SunboX/CO2-Ampel/Fotos/PXL_20201120_171447226.jpg

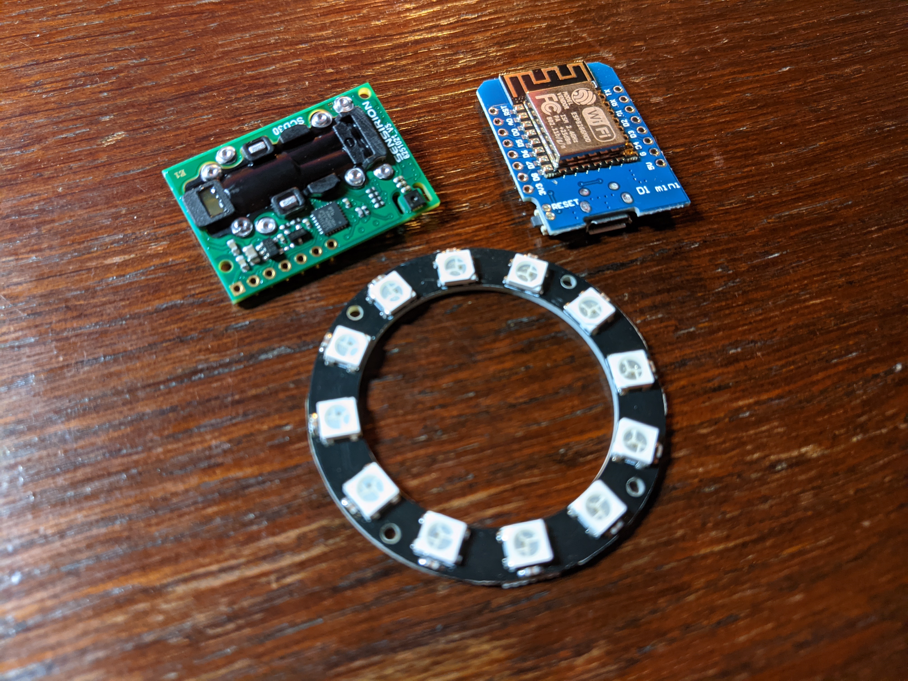
Fotos/PXL_20201120_171447226.jpg
