SunboX/CO2-Ampel/Fotos/PXL_20201120_172152929.jpg

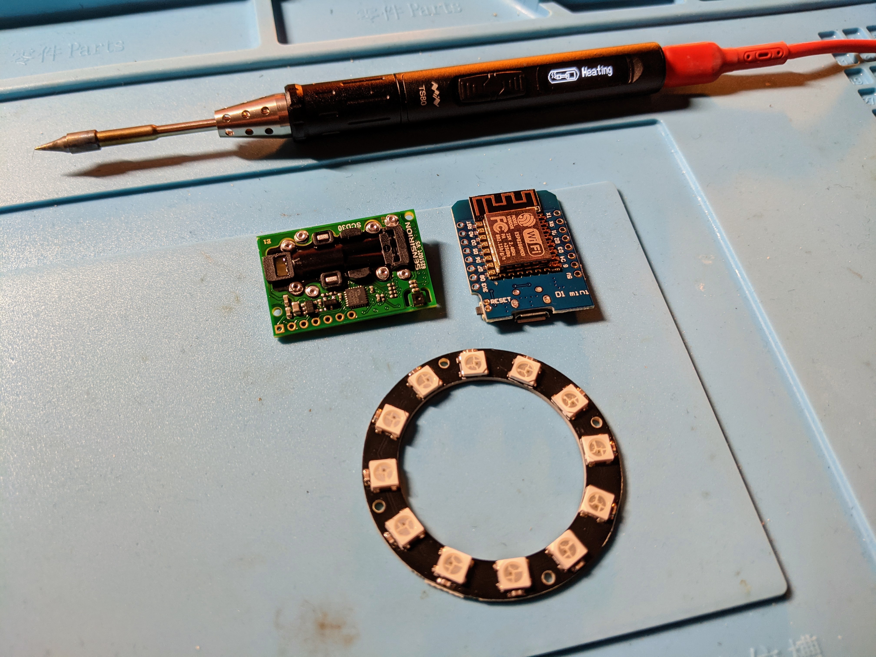
Fotos/PXL_20201120_172152929.jpg
