SunboX/CO2-Ampel/Fotos/PXL_20201120_174045806.jpg

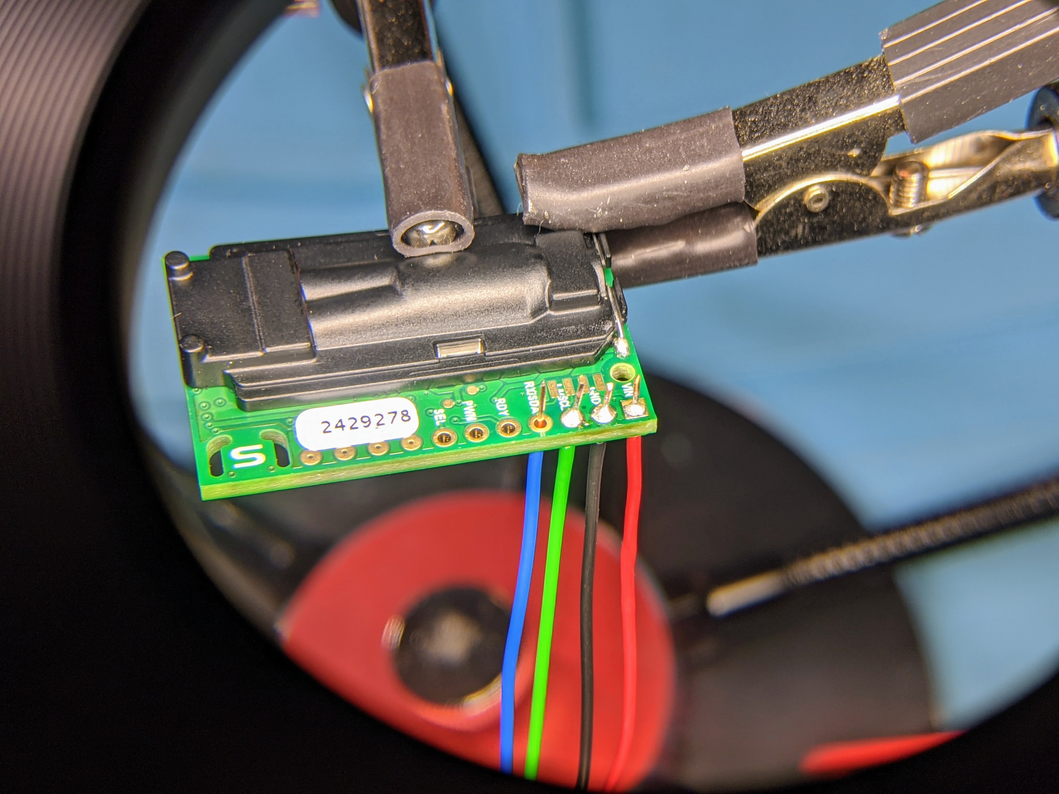
Fotos/PXL_20201120_174045806.jpg
