SunboX/CO2-Ampel/Fotos/PXL_20201120_174952225.jpg

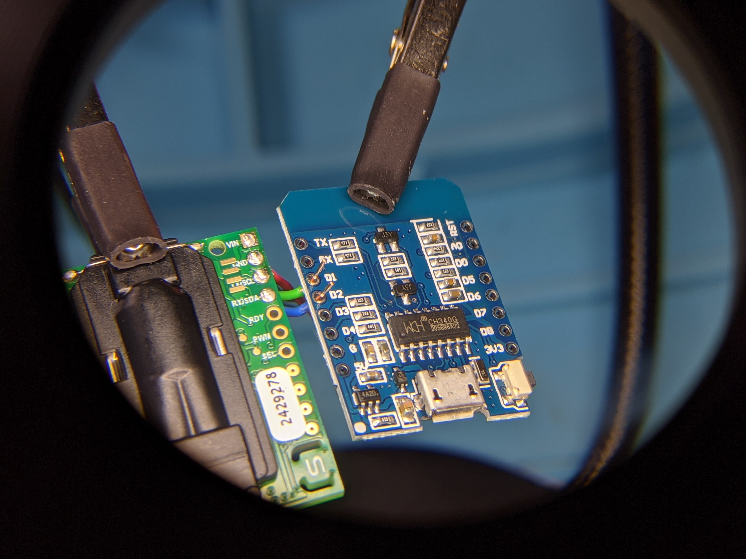
Fotos/PXL_20201120_174952225.jpg
