SunboX/CO2-Ampel/Fotos/PXL_20201120_175120646.jpg

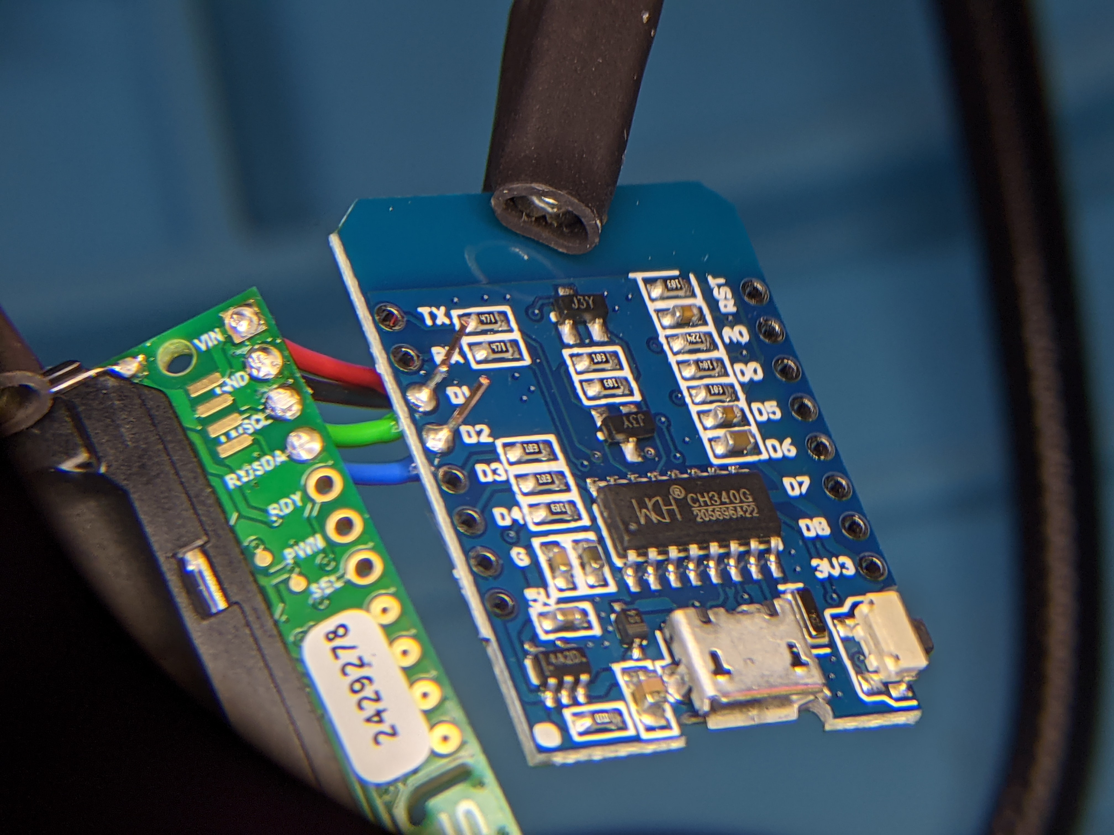
Fotos/PXL_20201120_175120646.jpg
