SunboX/CO2-Ampel/Fotos/PXL_20201121_131157792.jpg

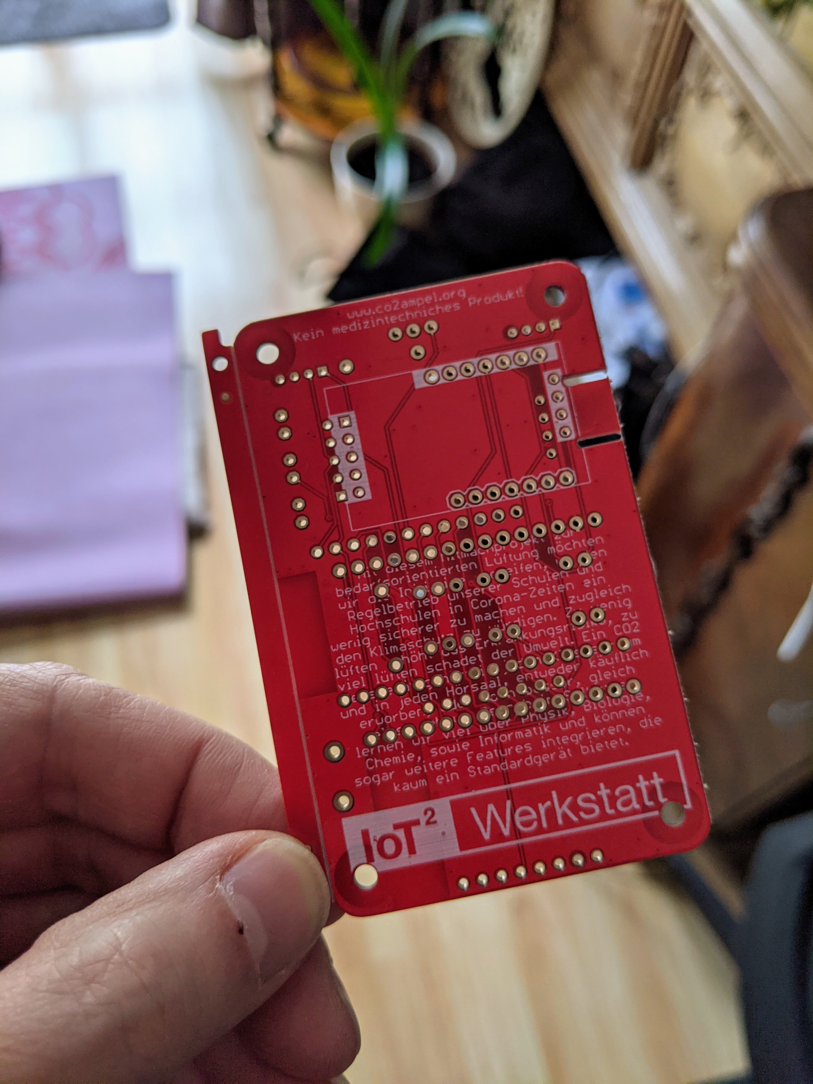
Fotos/PXL_20201121_131157792.jpg
