SunboX/CO2-Ampel/Fotos/PXL_20201121_131206932.jpg

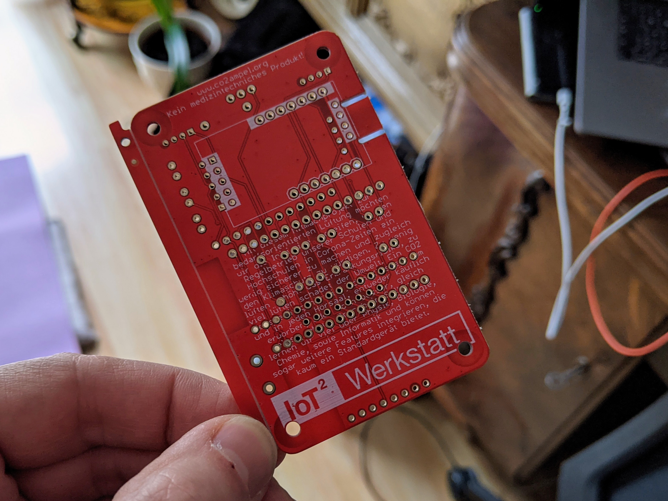
Fotos/PXL_20201121_131206932.jpg
