SunboX/CO2-Ampel/Fotos/PXL_20201121_220834875.jpg

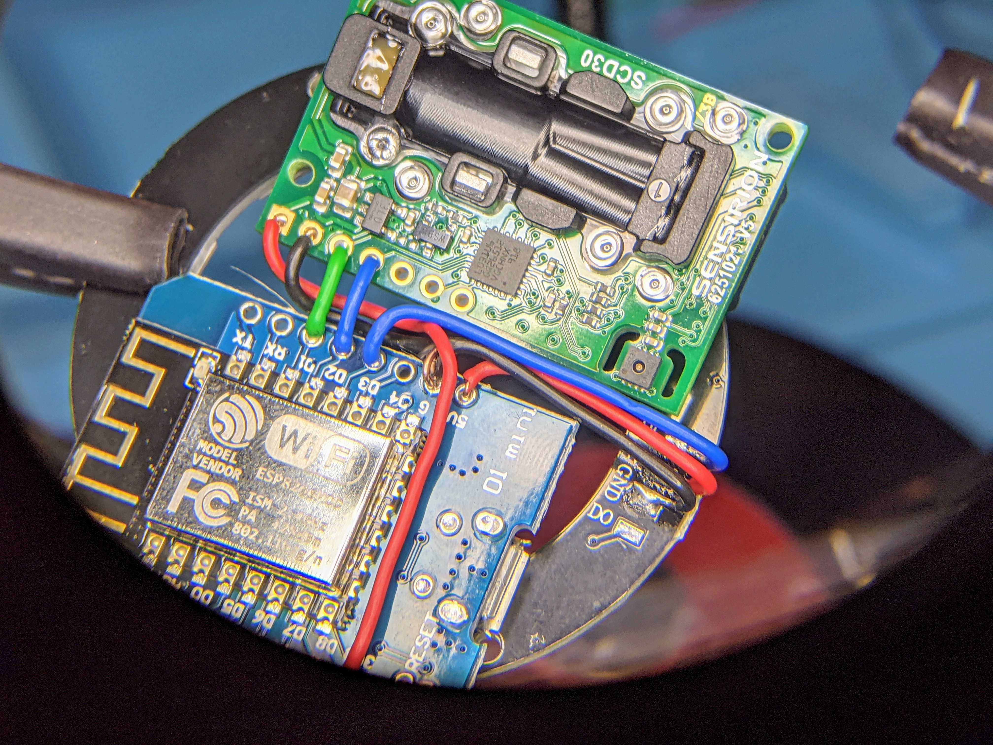
Fotos/PXL_20201121_220834875.jpg
