SunboX/CO2-Ampel/Fotos/PXL_20201121_220840101.jpg

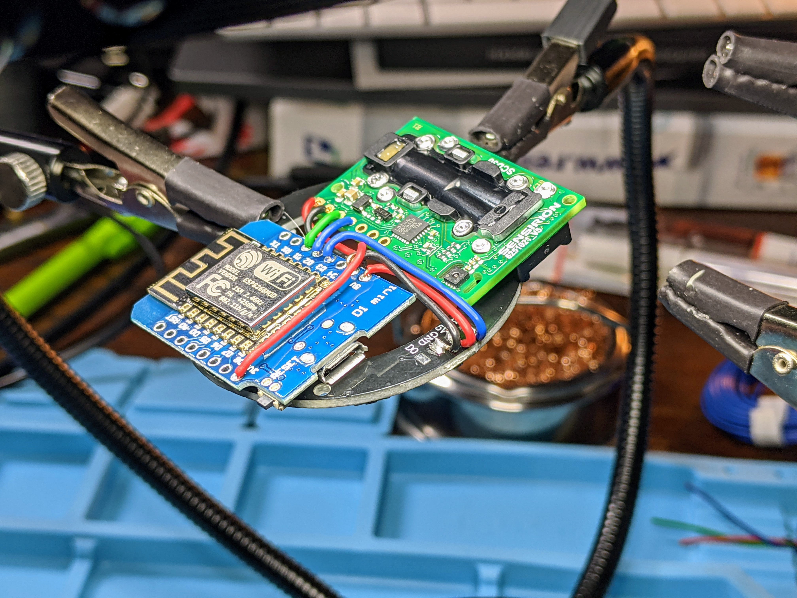
Fotos/PXL_20201121_220840101.jpg
