SunboX/CO2-Ampel/Fotos/PXL_20201121_220856868.jpg

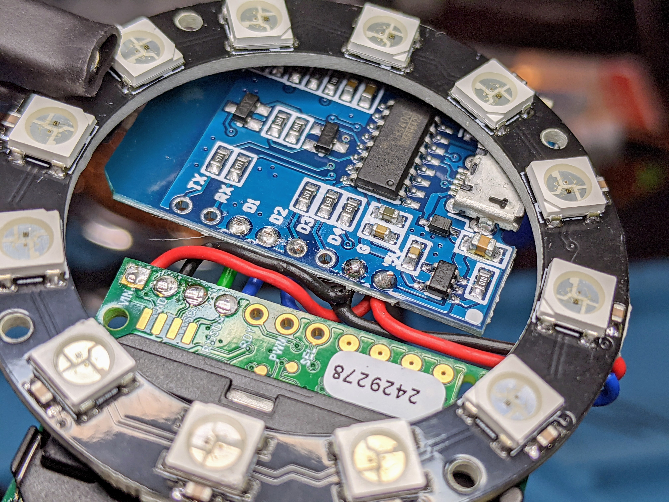
Fotos/PXL_20201121_220856868.jpg
