SunboX/CO2-Ampel/Fotos/PXL_20201121_220901508.jpg

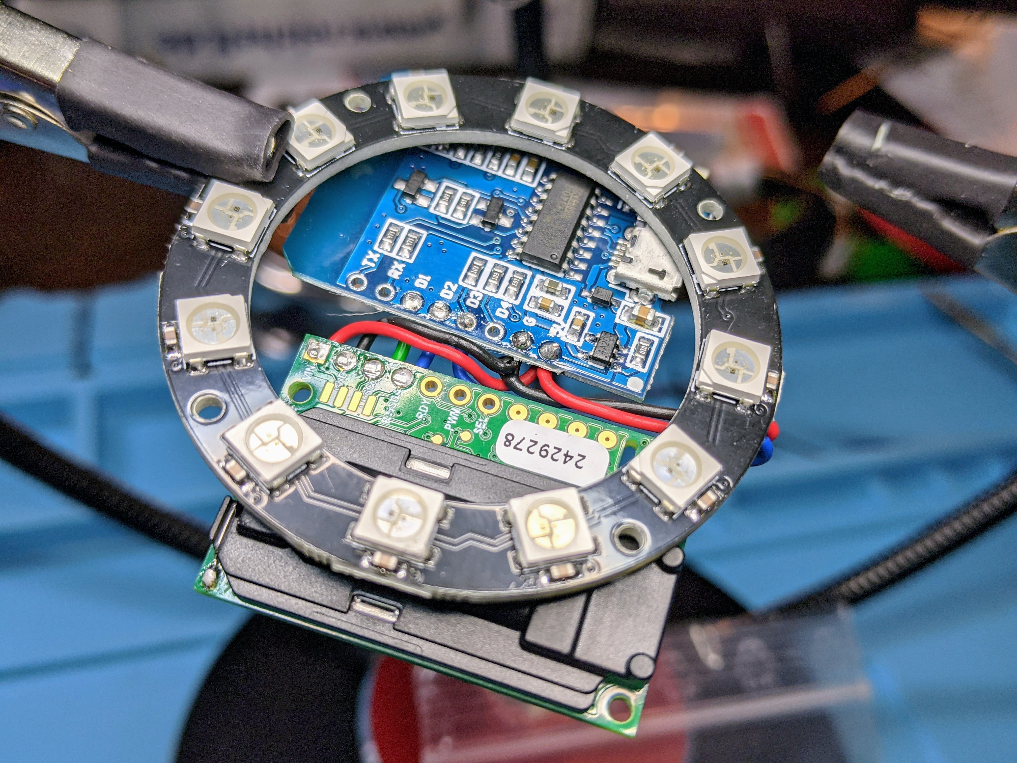
Fotos/PXL_20201121_220901508.jpg
