SunboX/CO2-Ampel/Fotos/PXL_20201121_220903162.jpg

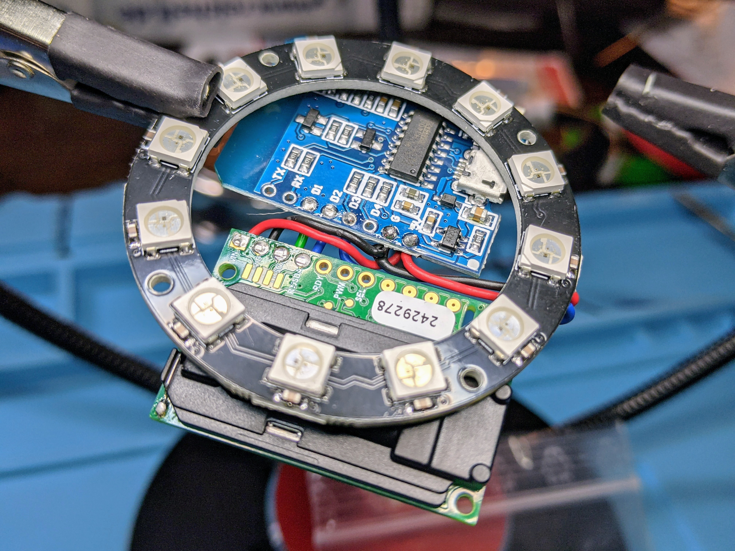
Fotos/PXL_20201121_220903162.jpg
