SunboX/CO2-Ampel/Fotos/PXL_20201121_221507168.jpg

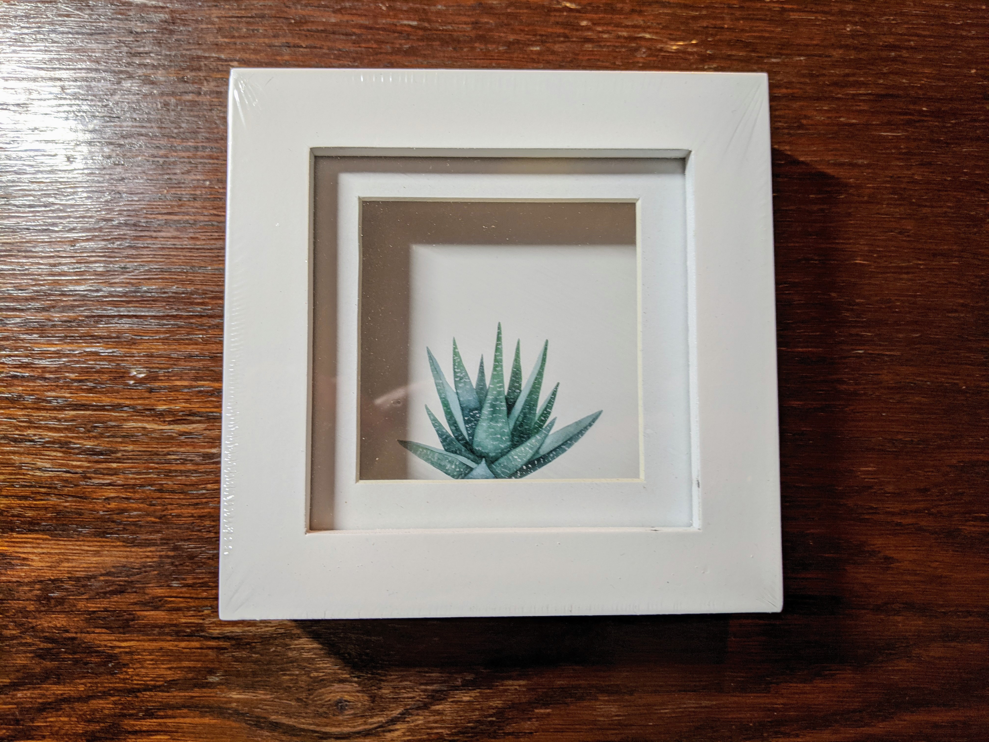
Fotos/PXL_20201121_221507168.jpg
