SunboX/CO2-Ampel/Fotos/PXL_20201121_221518086.jpg

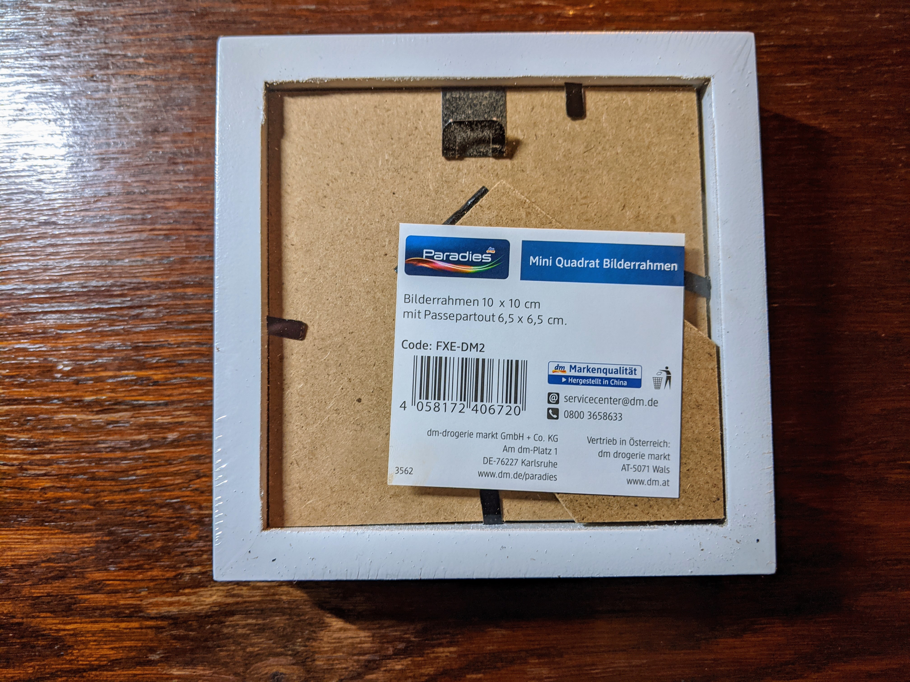
Fotos/PXL_20201121_221518086.jpg
