SunboX/CO2-Ampel/Fotos/PXL_20201121_221521341.jpg

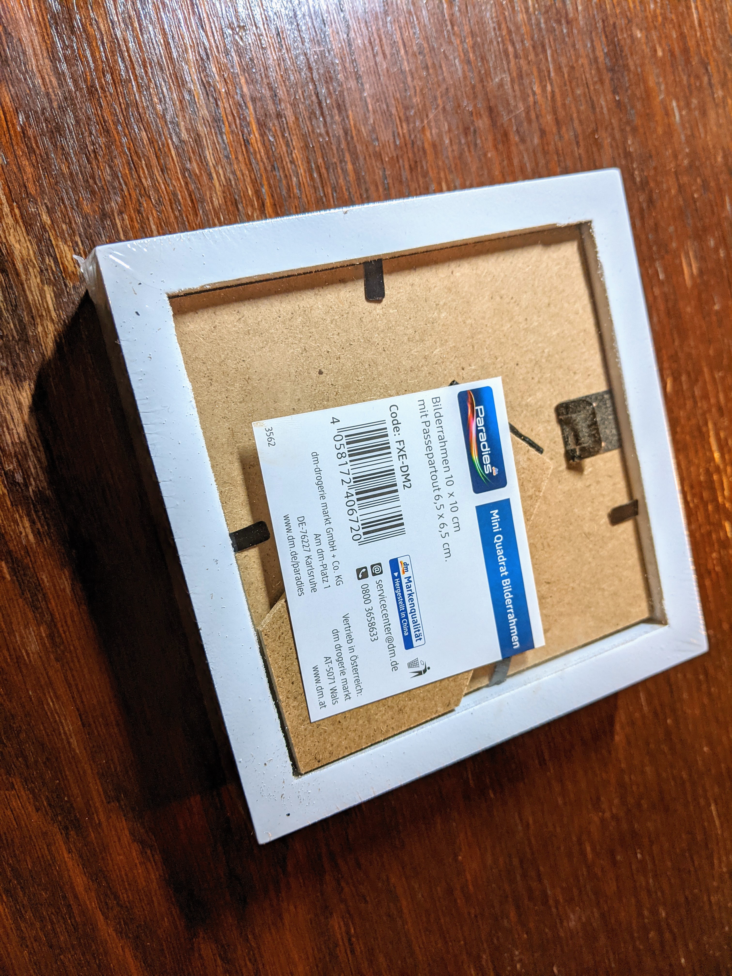
Fotos/PXL_20201121_221521341.jpg
