SunboX/CO2-Ampel/Fotos/PXL_20201121_221523429.jpg

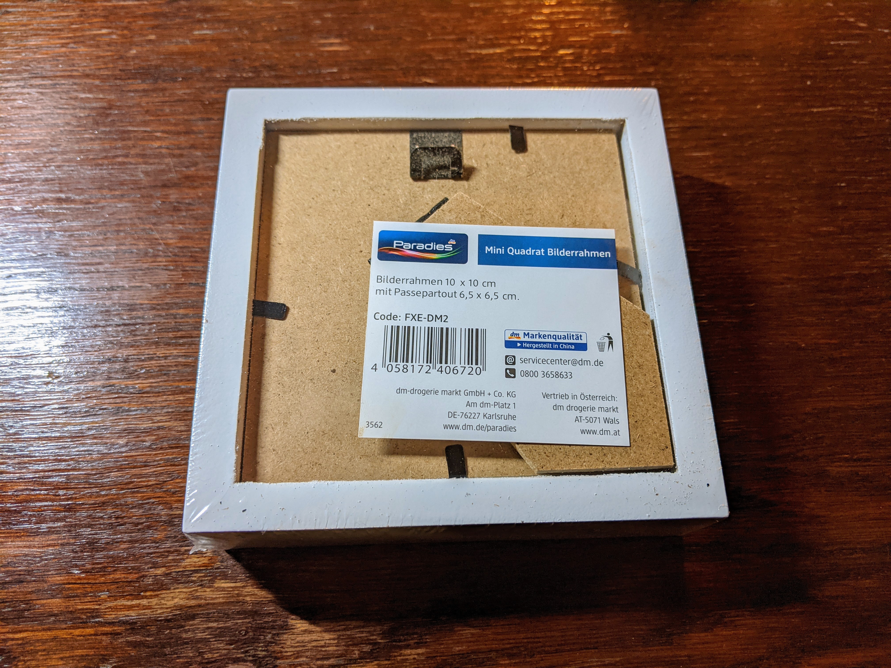
Fotos/PXL_20201121_221523429.jpg
