SunboX/CO2-Ampel/Fotos/PXL_20201121_221529776.jpg

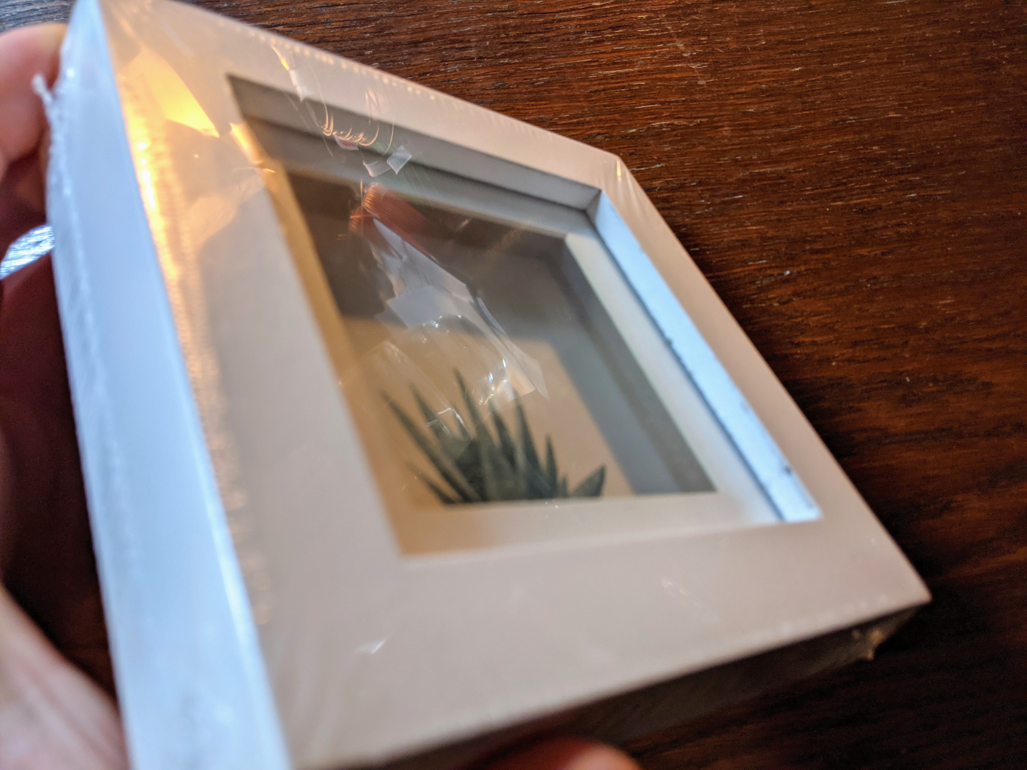
Fotos/PXL_20201121_221529776.jpg
