SunboX/CO2-Ampel/Fotos/PXL_20201121_221532675.jpg

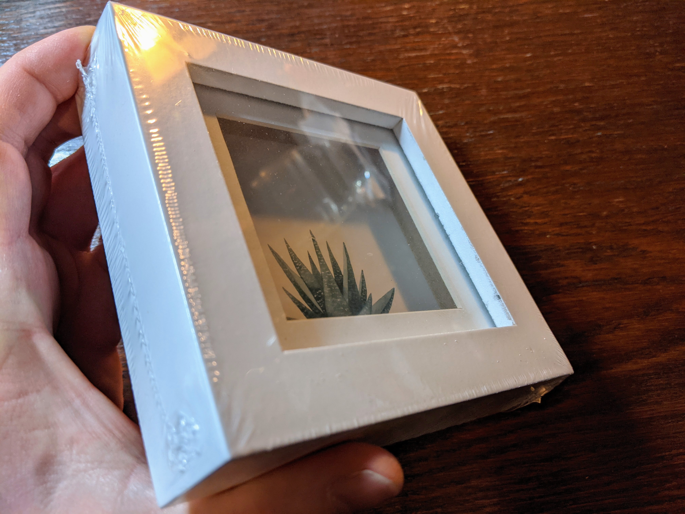
Fotos/PXL_20201121_221532675.jpg
