SunboX/CO2-Ampel/Fotos/PXL_20201121_232246506.jpg

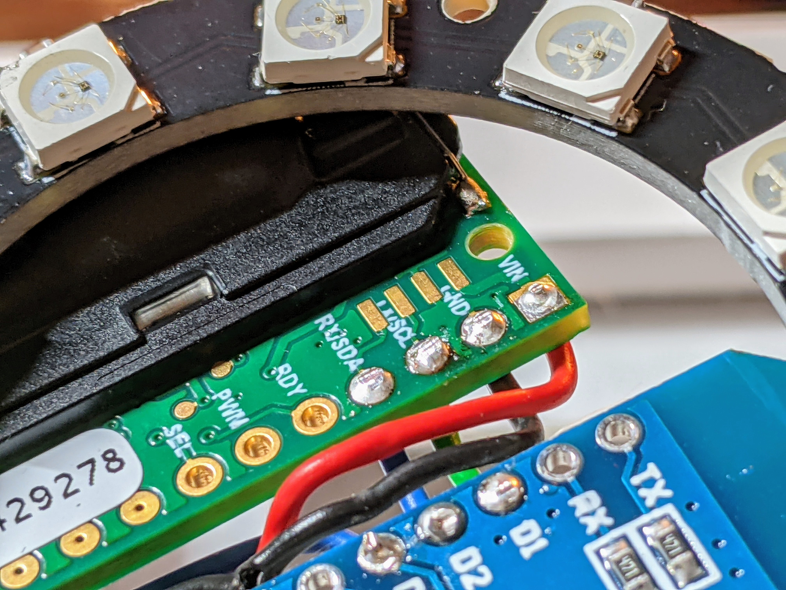
Fotos/PXL_20201121_232246506.jpg
