SunboX/CO2-Ampel/Fotos/PXL_20201122_005400794.jpg

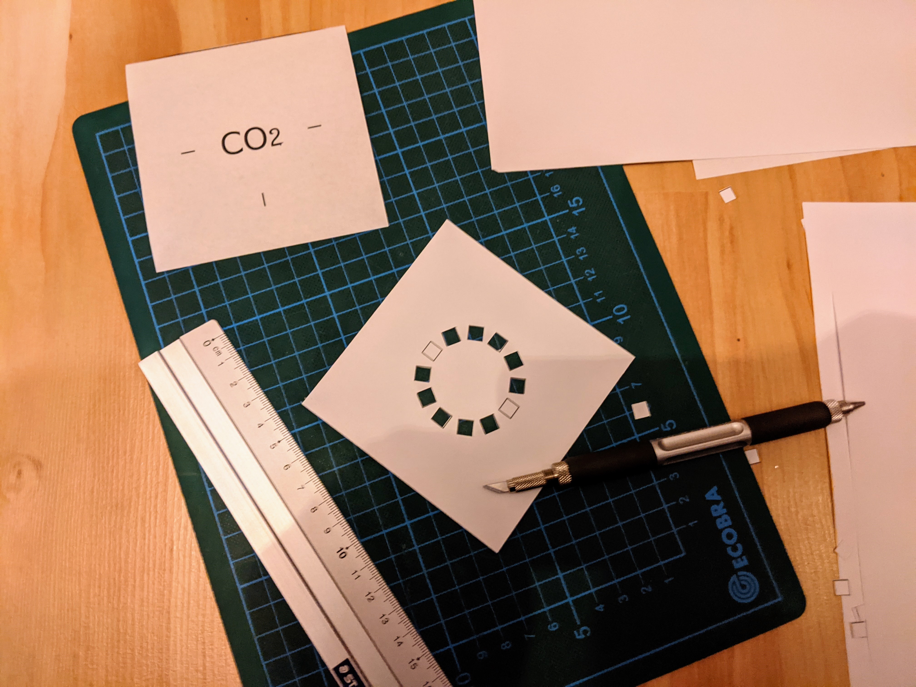
Fotos/PXL_20201122_005400794.jpg
