SunboX/CO2-Ampel/Fotos/PXL_20201122_005405418.jpg

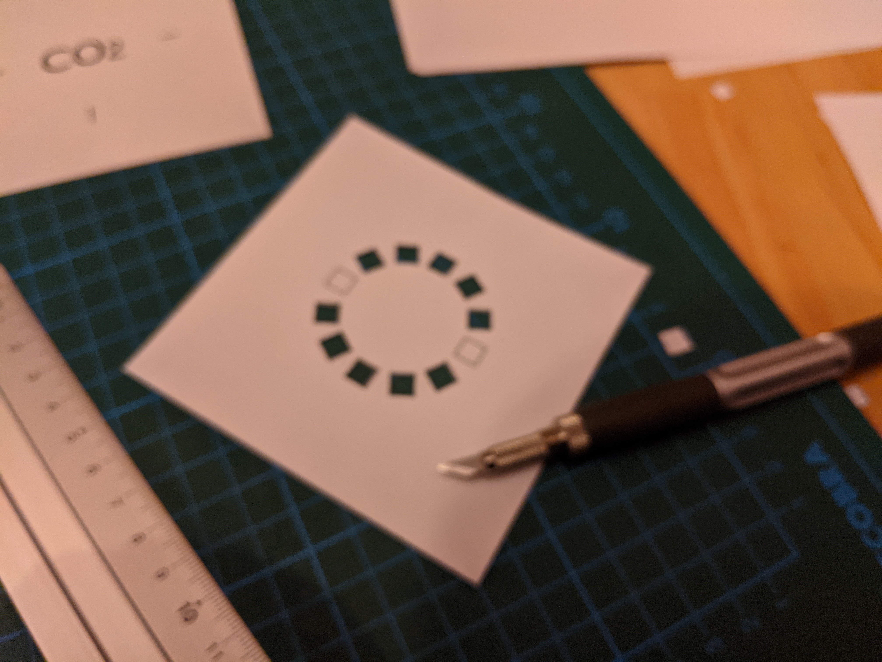
Fotos/PXL_20201122_005405418.jpg
