SunboX/CO2-Ampel/Fotos/PXL_20201122_005413096.jpg

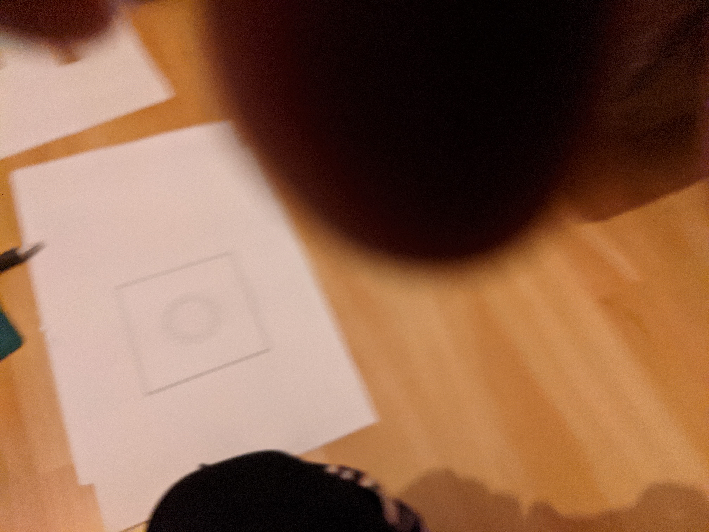
Fotos/PXL_20201122_005413096.jpg
