SunboX/CO2-Ampel/Fotos/PXL_20201122_010641004.jpg

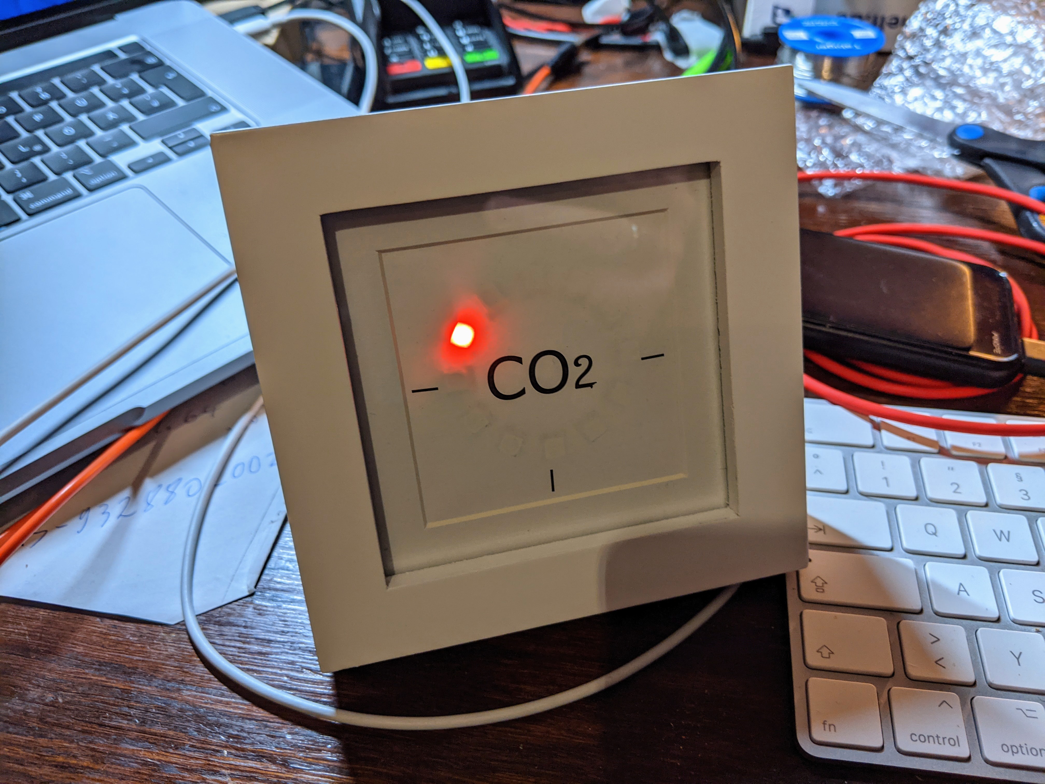
Fotos/PXL_20201122_010641004.jpg
