SunboX/CO2-Ampel/Fotos/PXL_20201122_011531768.jpg

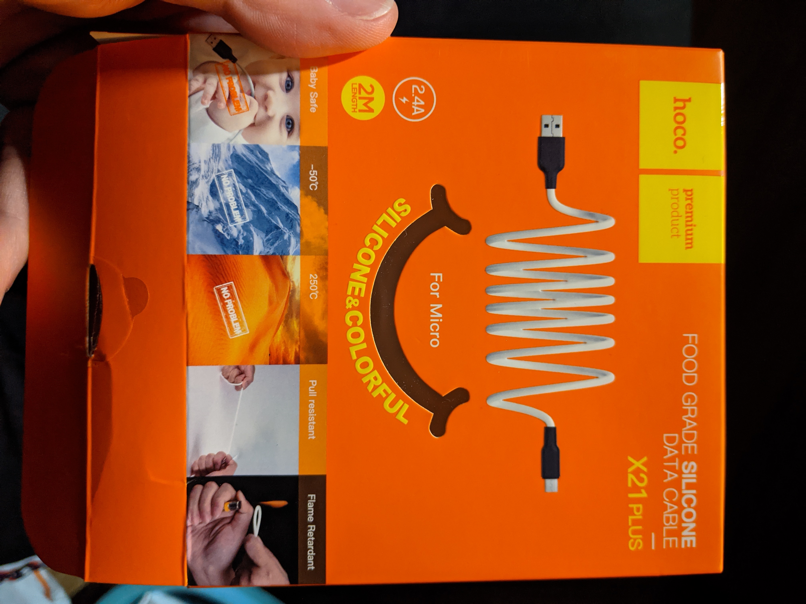
Fotos/PXL_20201122_011531768.jpg
