SunboX/CO2-Ampel/Fotos/PXL_20201122_013820252.jpg

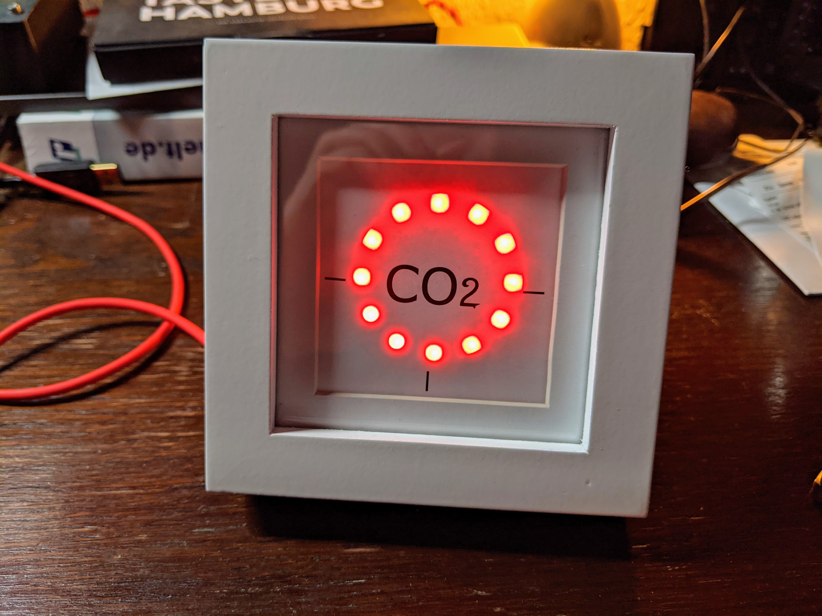
Fotos/PXL_20201122_013820252.jpg
