SunboX/CO2-Ampel/Fotos/PXL_20201122_013822471.jpg

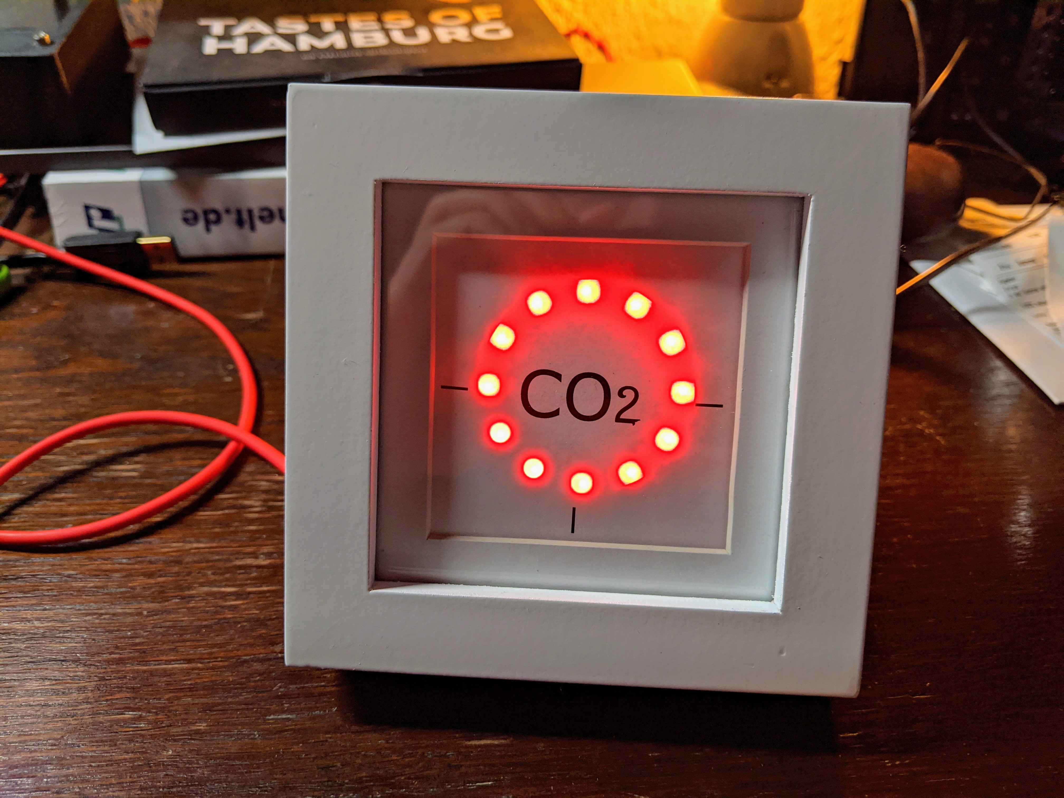
Fotos/PXL_20201122_013822471.jpg
