SunboX/CO2-Ampel/Fotos/PXL_20201122_014247296.jpg

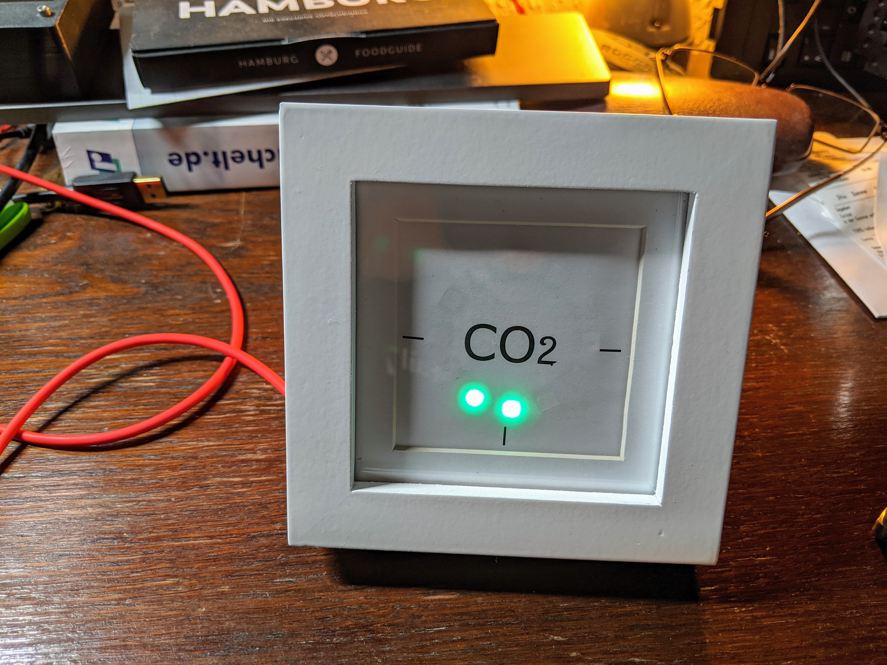
Fotos/PXL_20201122_014247296.jpg
