SunboX/CO2-Ampel/Fotos/PXL_20201122_014259222.jpg

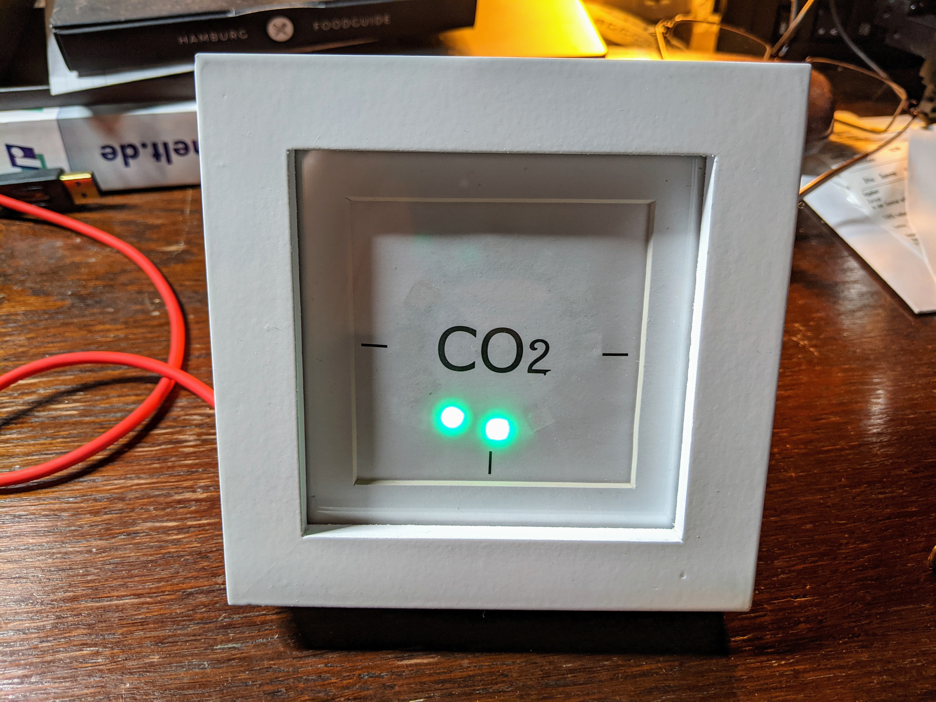
Fotos/PXL_20201122_014259222.jpg
